bruno2-ventilator/bruno2/Design Materials/Mechanical/Adapters/1:4 NPT to 3:4-inch barb/1:4 NPT to 3:4-inch barb.png

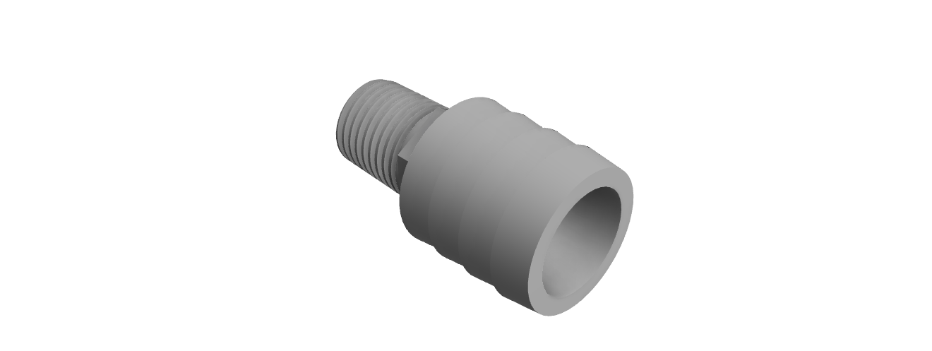
Design Materials/Mechanical/Adapters/1:4 NPT to 3:4-inch barb/1:4 NPT to 3:4-inch barb.png
