bruno2-ventilator/bruno2/Design Materials/Mechanical/Pinch Valves/Cam Valve/STL/Roller Undersize.STL

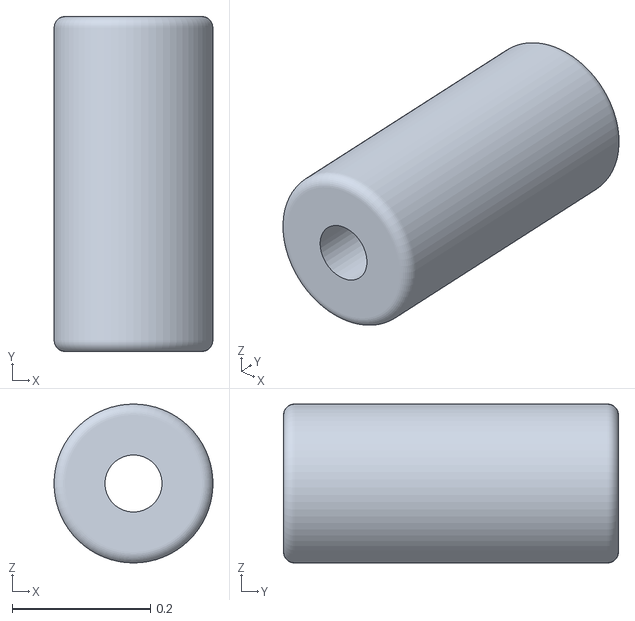
[picture p48: CAD file, 2020-04-19]
Design Materials/Mechanical/Pinch Valves/Cam Valve/STL/Roller Undersize.STL
0.23 x 0.485 x 0.23
