bruno2-ventilator/bruno2/Design Materials/Mechanical/Pinch Valves/Cam Valve/STEP/Top.STEP

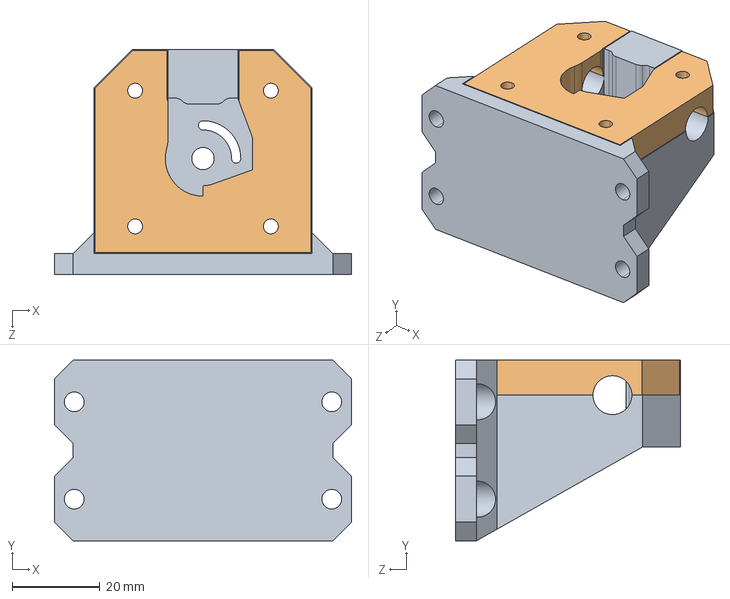
[picture p49: CAD file, 2020-04-19]
Design Materials/Mechanical/Pinch Valves/Cam Valve/STEP/Top.STEP
67.8 x 41.3 x 51.4 mm
