bruno2-ventilator/bruno2/Design Materials/Mechanical/Pinch Valves/Cam Valve/SLDPRT/0.375 Tubing.SLDPRT

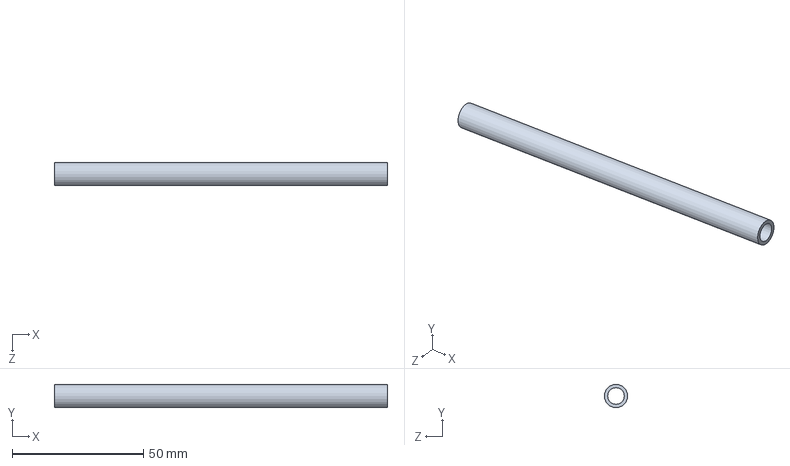
[picture p50: CAD file, 2020-04-19]
Design Materials/Mechanical/Pinch Valves/Cam Valve/SLDPRT/0.375 Tubing.SLDPRT
127.0 x 8.89 x 8.89 mm
