bruno2-ventilator/bruno2/Design Materials/Mechanical/Pinch Valves/Cam Valve/SLDPRT/M3x22 SHCP.SLDPRT

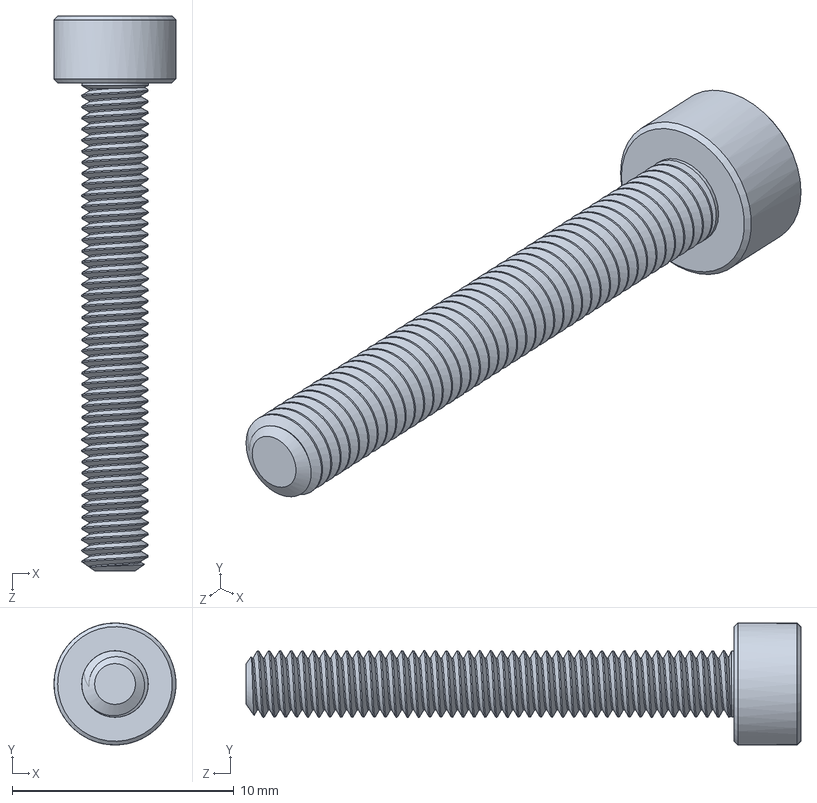
[picture p51: CAD file, 2020-04-19]
Design Materials/Mechanical/Pinch Valves/Cam Valve/SLDPRT/M3x22 SHCP.SLDPRT
5.50 x 5.50 x 25.0 mm
